BaileyBrookes/Part_IIB_Project/Code/Plots/11-11-18_Base_Still_Satellties.png

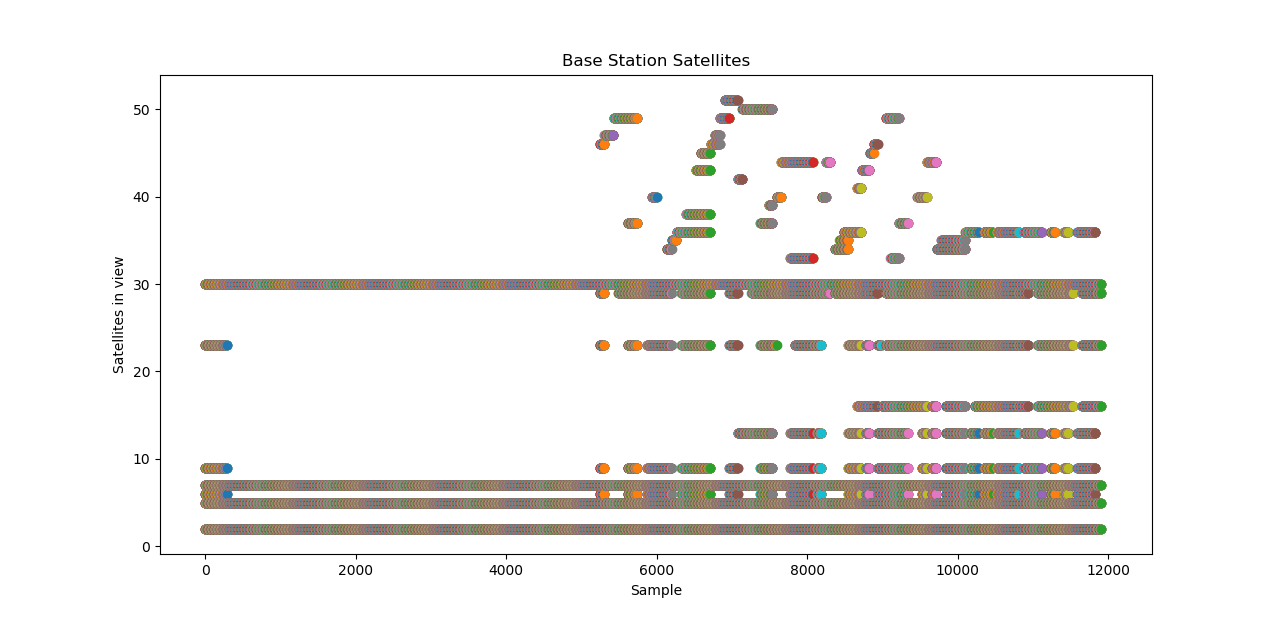
Code/Plots/11-11-18_Base_Still_Satellties.png
