BaileyBrookes/Part_IIB_Project/Code/Plots/11-11-18_WALK.png

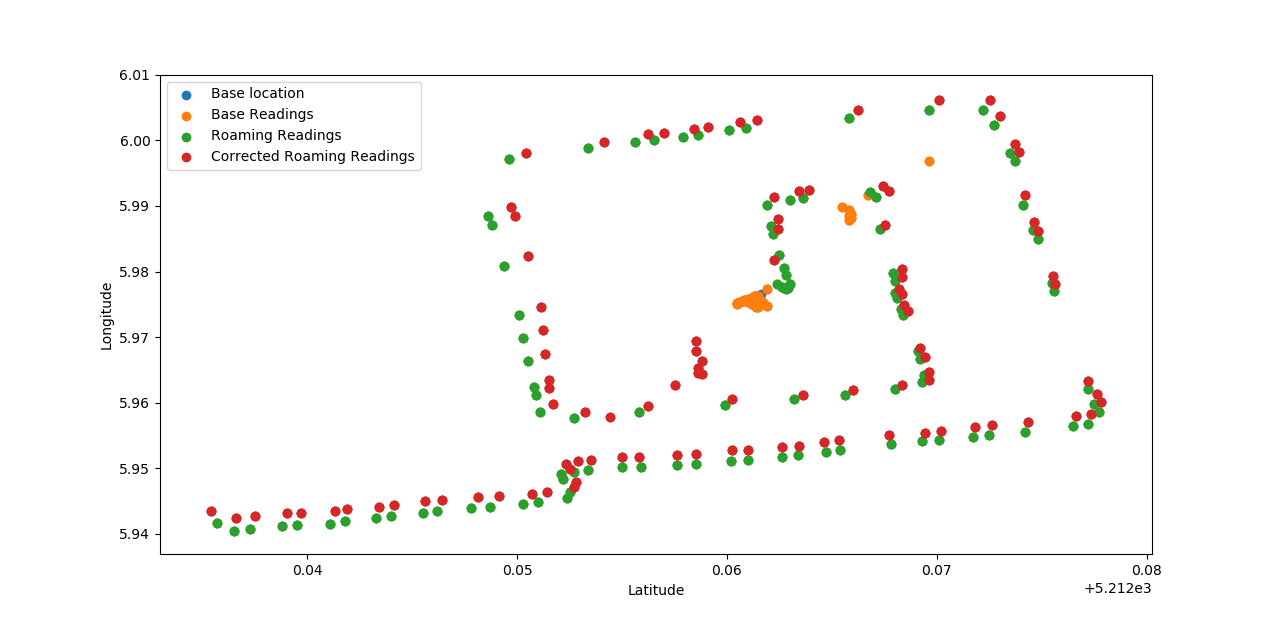
Code/Plots/11-11-18_WALK.png
