BaileyBrookes/Part_IIB_Project/Code/Plots/Figure_1.png

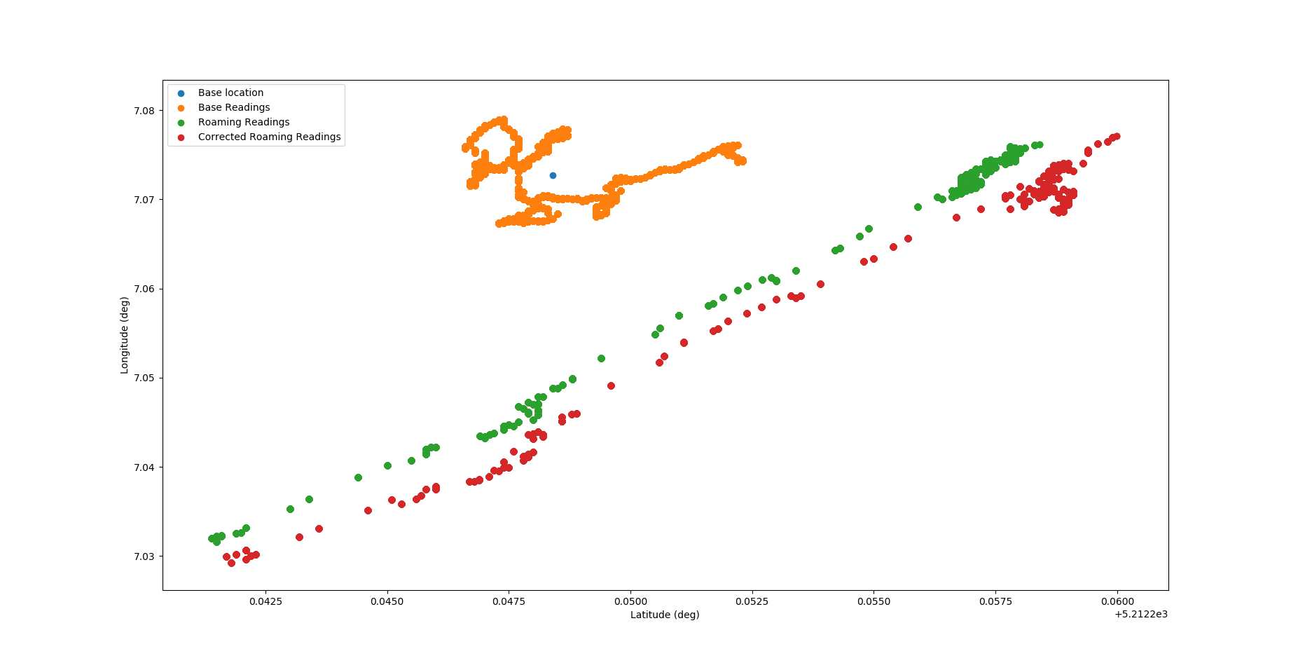
Code/Plots/Figure_1.png
