BaileyBrookes/Part_IIB_Project/Final Report/Castle_hill.png

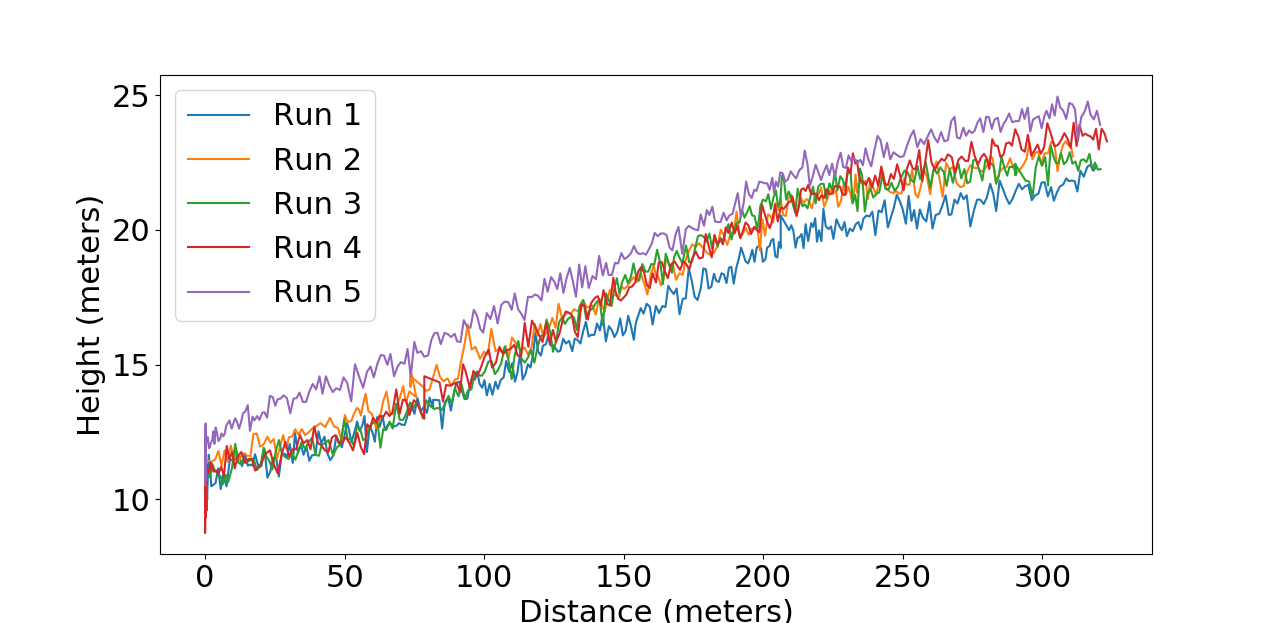
Final Report/Castle_hill.png
