BaileyBrookes/Part_IIB_Project/Final Report/Circuit_annotate.png

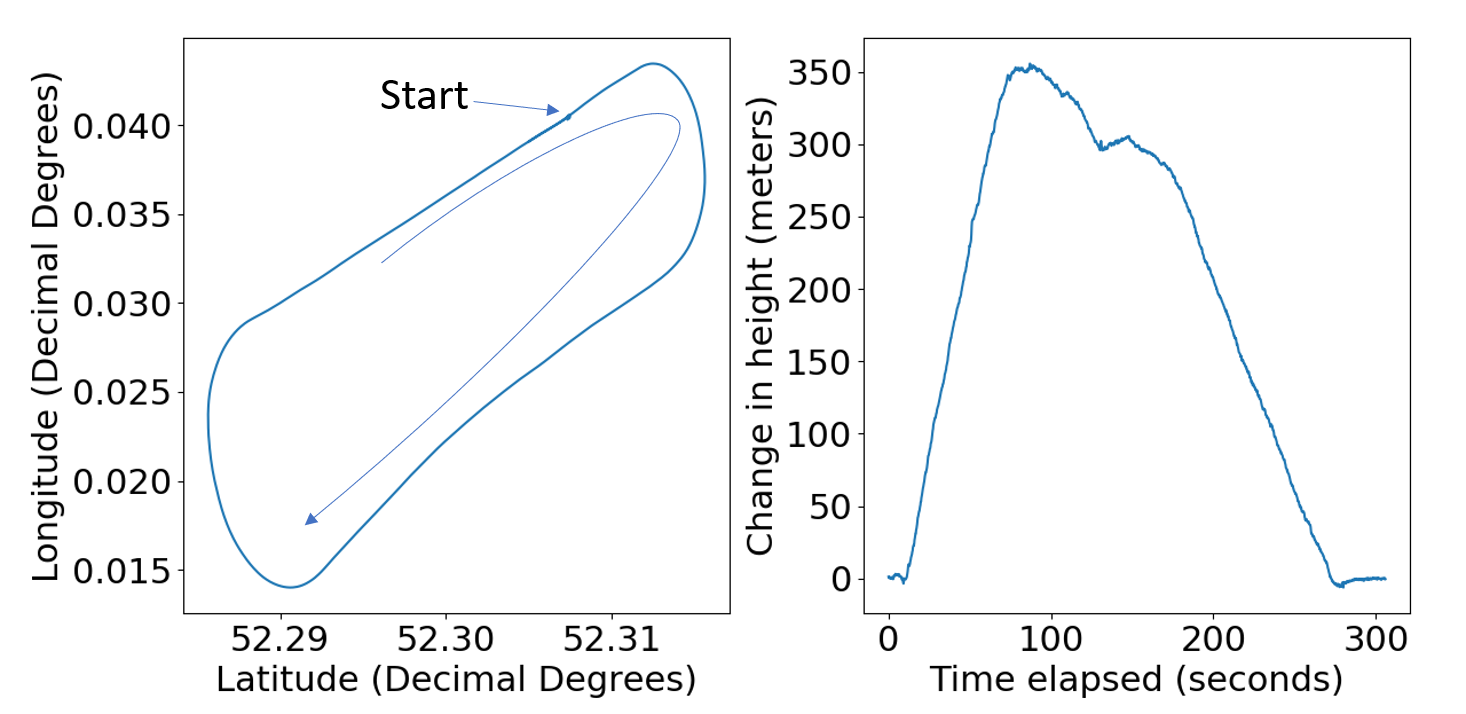
Final Report/Circuit_annotate.png
