BaileyBrookes/Part_IIB_Project/Final Report/Circuit_schematic.png

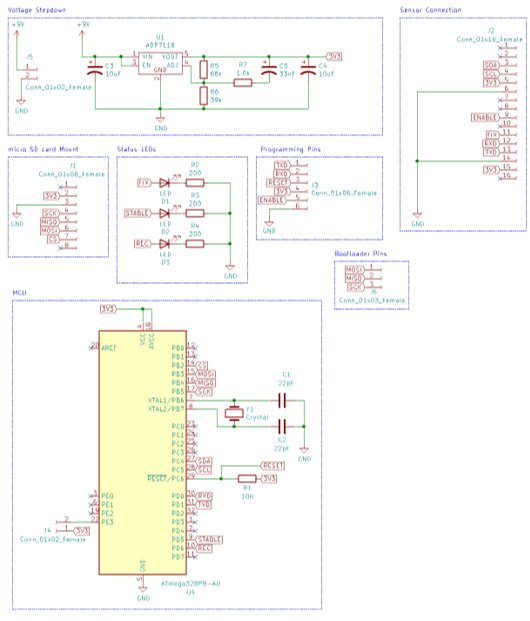
Final Report/Circuit_schematic.png
