BaileyBrookes/Part_IIB_Project/Final Report/Flight_path.png

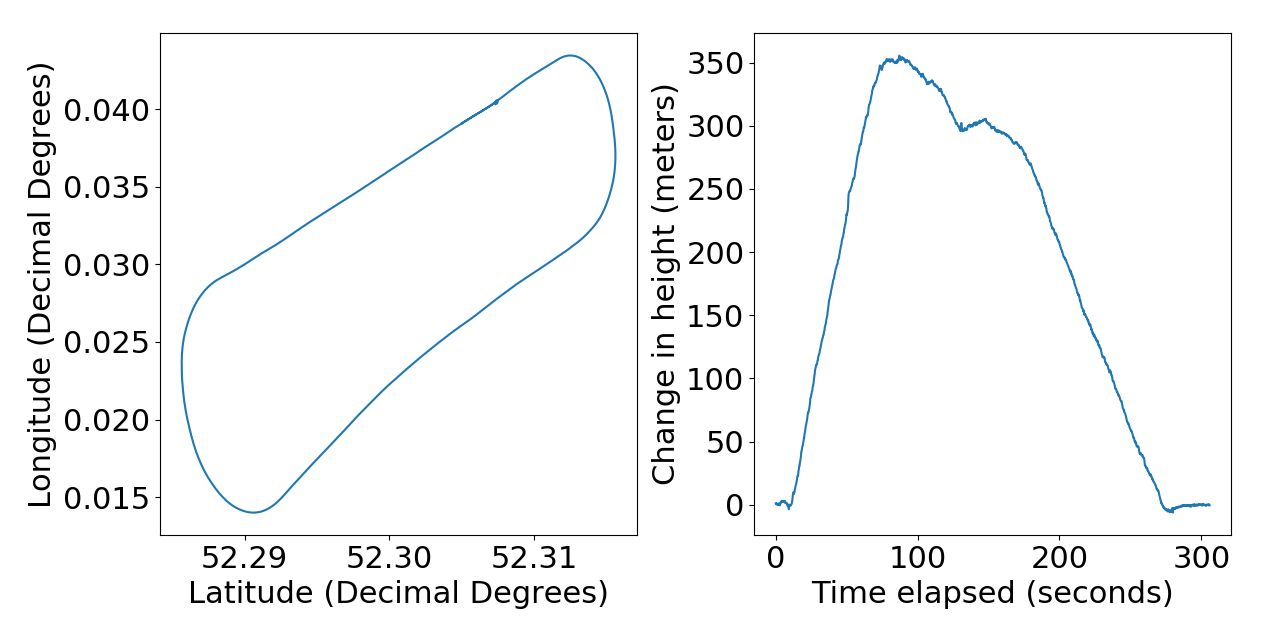
Final Report/Flight_path.png
