BaileyBrookes/Part_IIB_Project/Final Report/GPS_and_altimeter_height.png

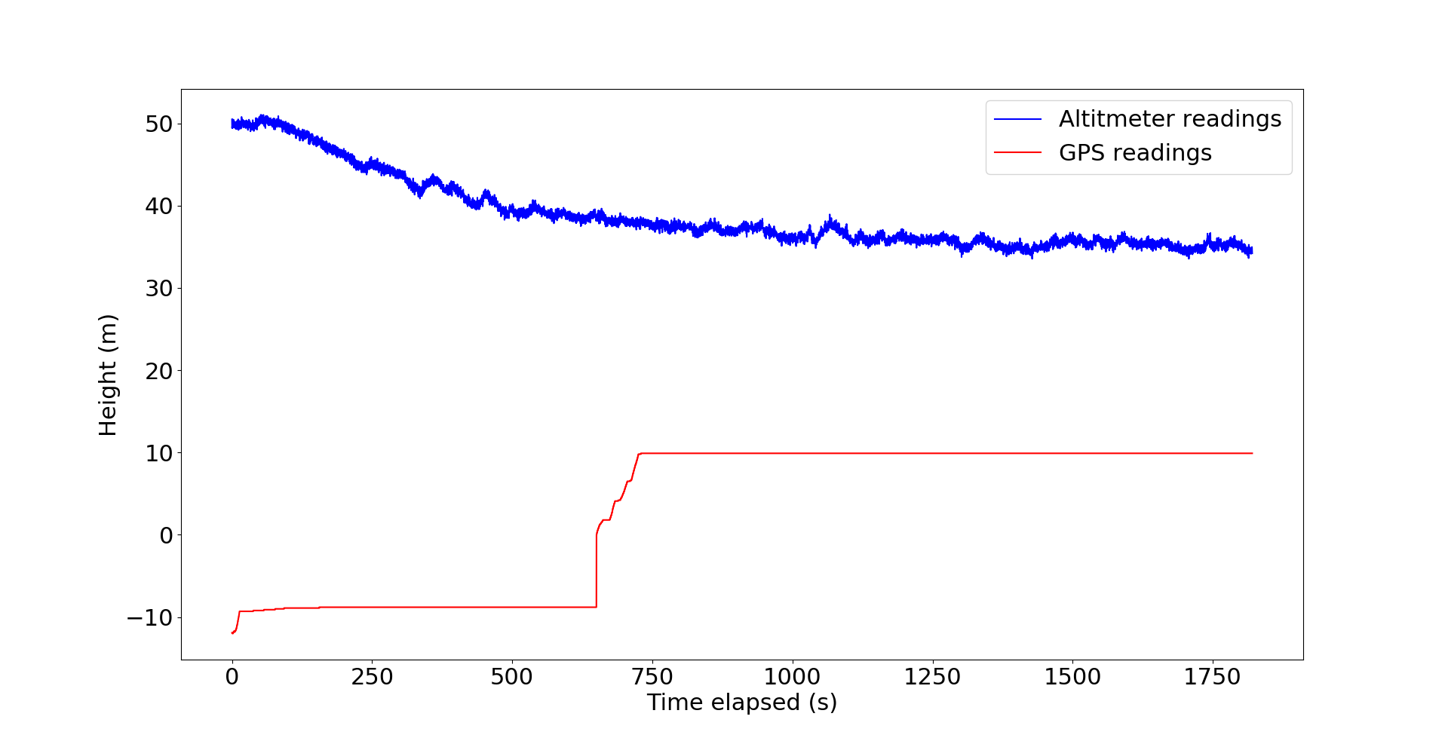
Final Report/GPS_and_altimeter_height.png
