BaileyBrookes/Part_IIB_Project/Final Report/IMG_20190519_162821.jpg

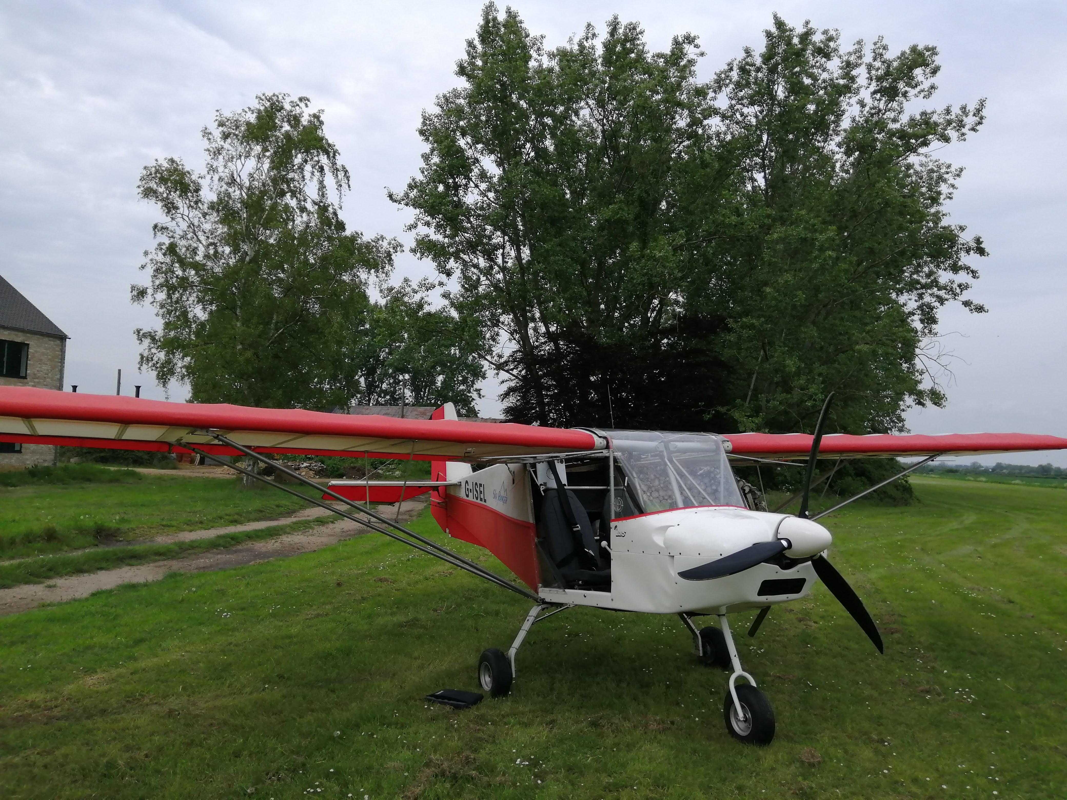
Final Report/IMG_20190519_162821.jpg
