BaileyBrookes/Part_IIB_Project/Final Report/IMG_20190520_114710.jpg

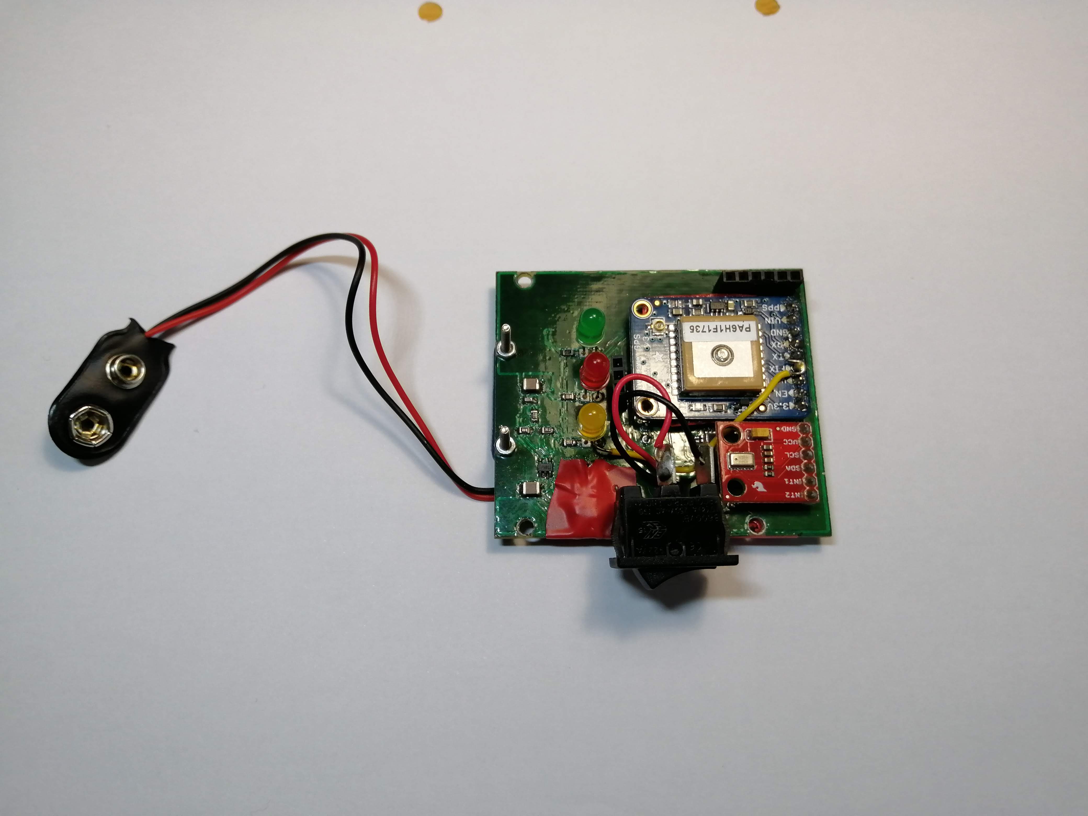
Final Report/IMG_20190520_114710.jpg
