BaileyBrookes/Part_IIB_Project/Final Report/IMG_20190520_114843.jpg

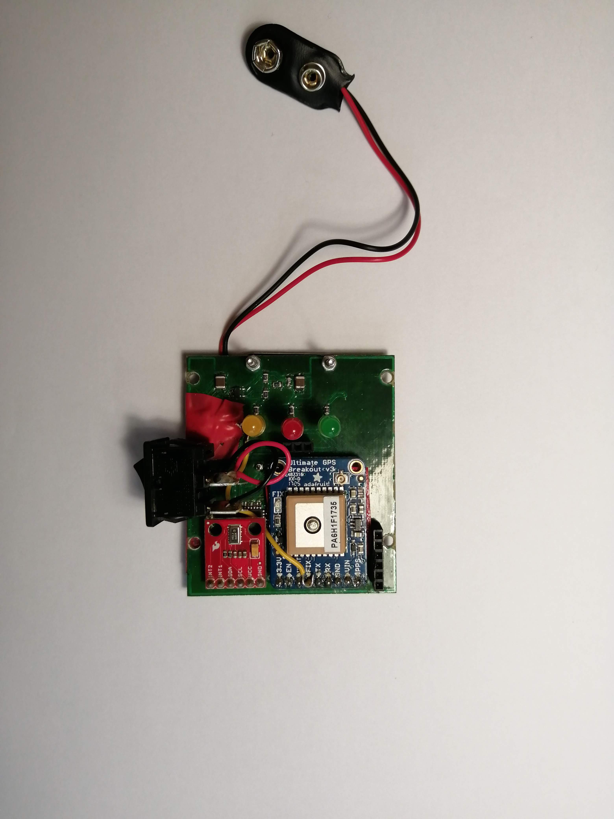
Final Report/IMG_20190520_114843.jpg
