BaileyBrookes/Part_IIB_Project/Final Report/IMG_20190520_114852.jpg

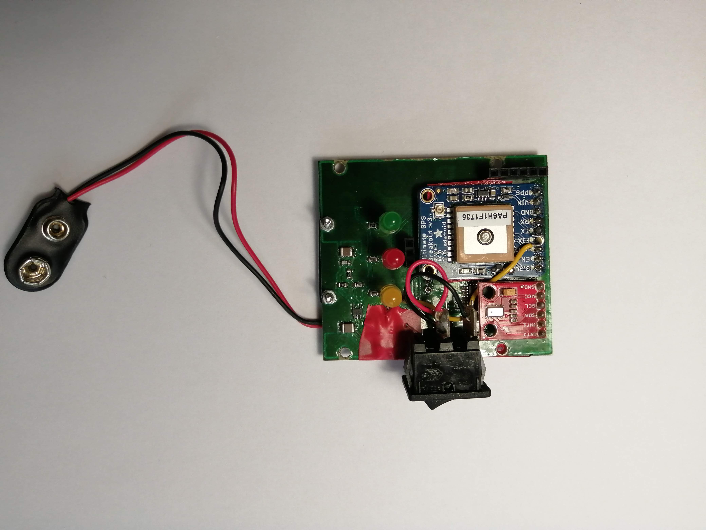
Final Report/IMG_20190520_114852.jpg
