BaileyBrookes/Part_IIB_Project/Final Report/IMG_20190520_115139.jpg

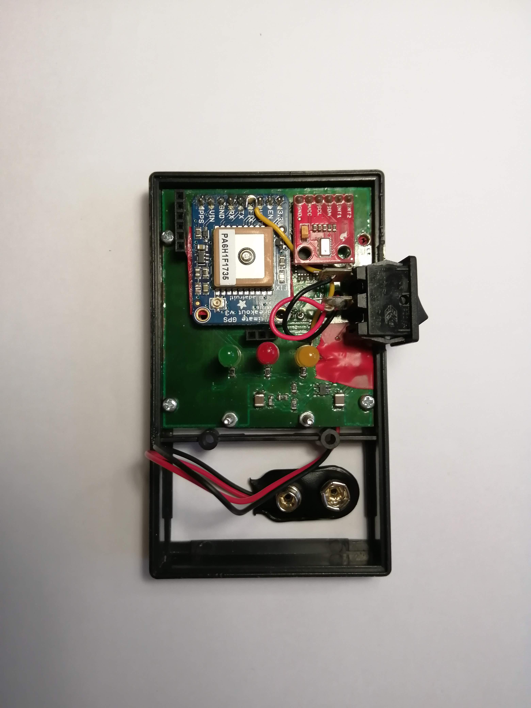
Final Report/IMG_20190520_115139.jpg
