BaileyBrookes/Part_IIB_Project/Final Report/IMG_20190520_115651.jpg

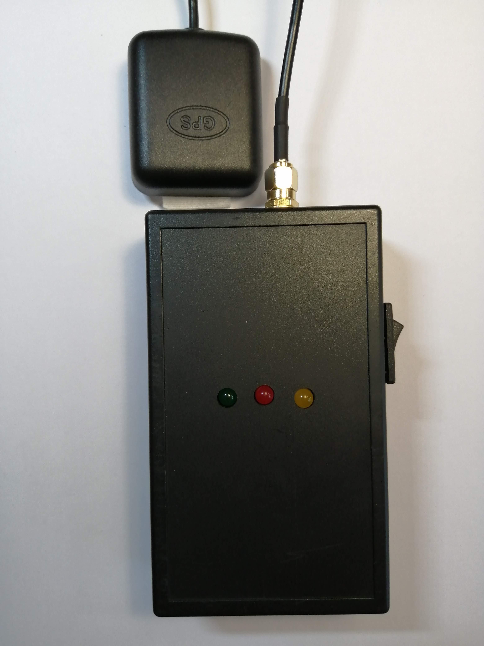
Final Report/IMG_20190520_115651.jpg
