BaileyBrookes/Part_IIB_Project/Final Report/jump.png

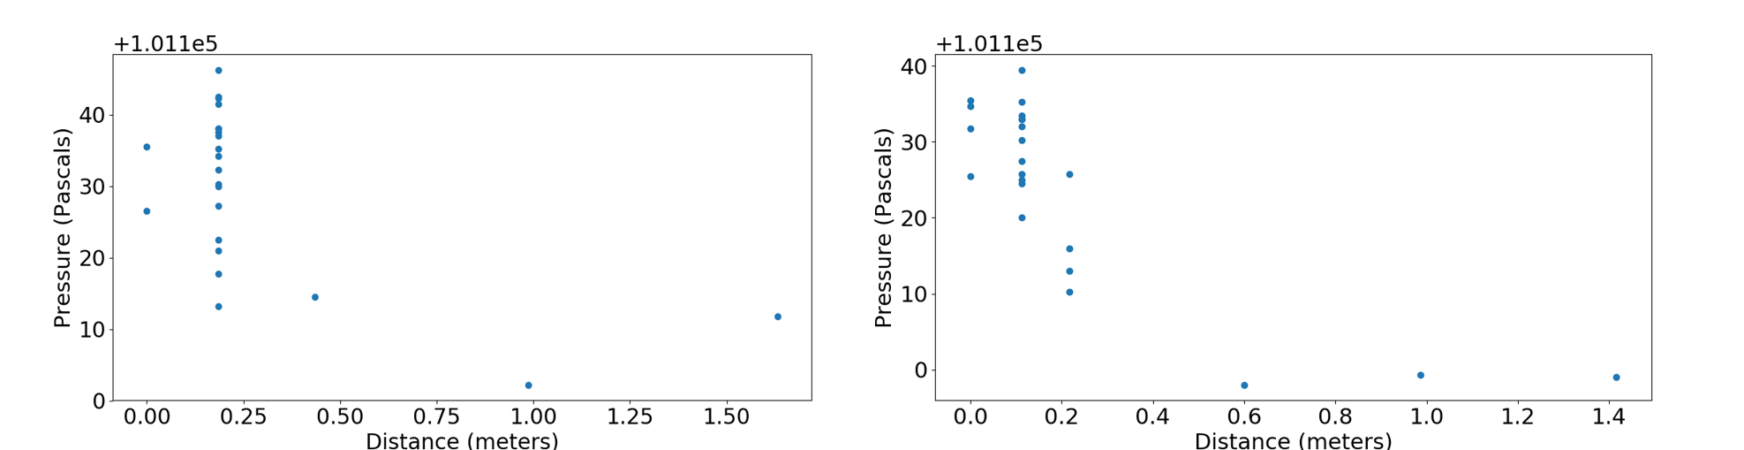
Final Report/jump.png
