BaileyBrookes/Part_IIB_Project/Final Report/Landing_flight_1.png

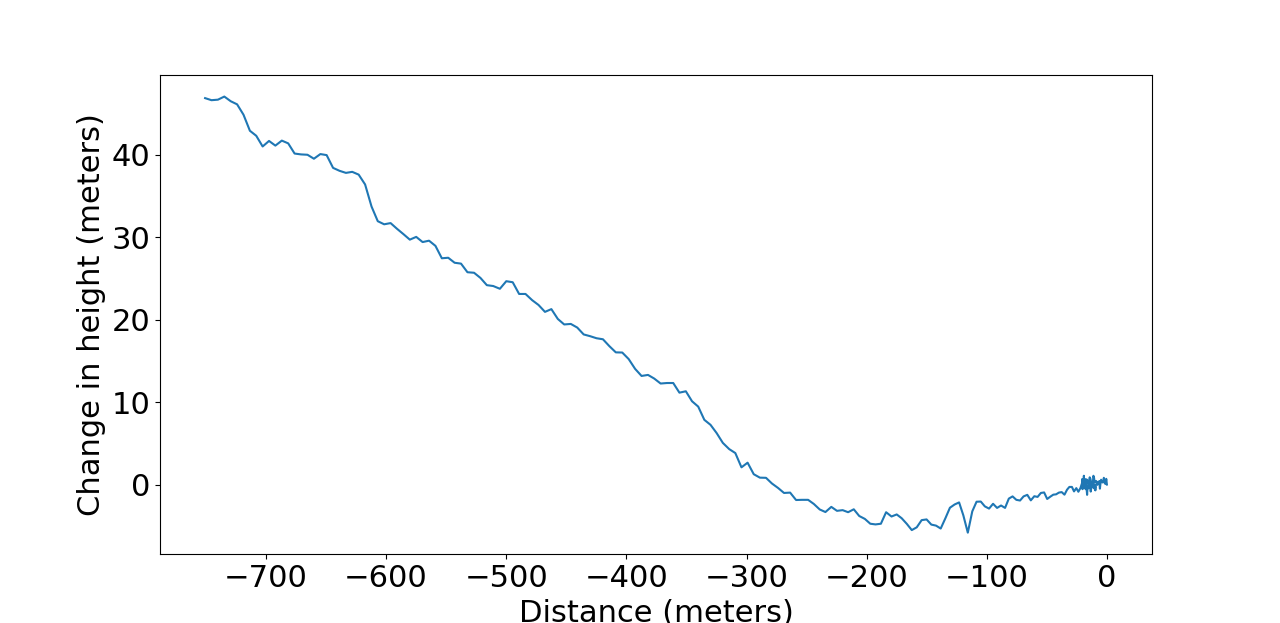
Final Report/Landing_flight_1.png
