BaileyBrookes/Part_IIB_Project/Final Report/Leck_100m_4.png

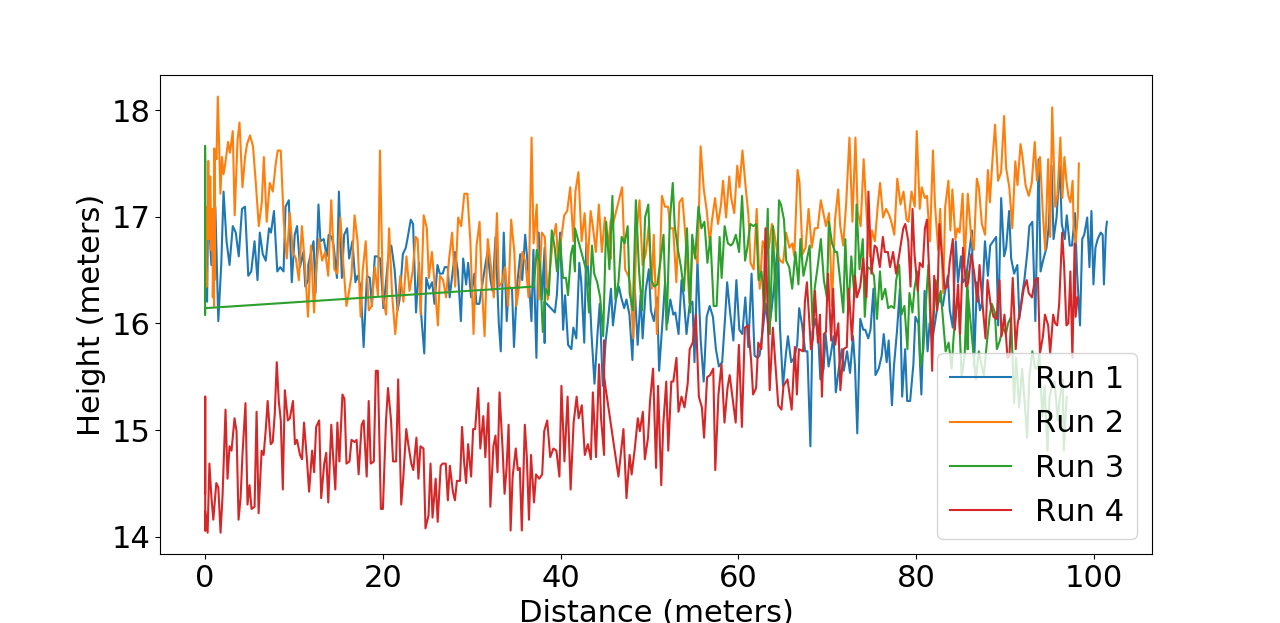
Final Report/Leck_100m_4.png
