BaileyBrookes/Part_IIB_Project/Final Report/Leck_GPS_Pres.png

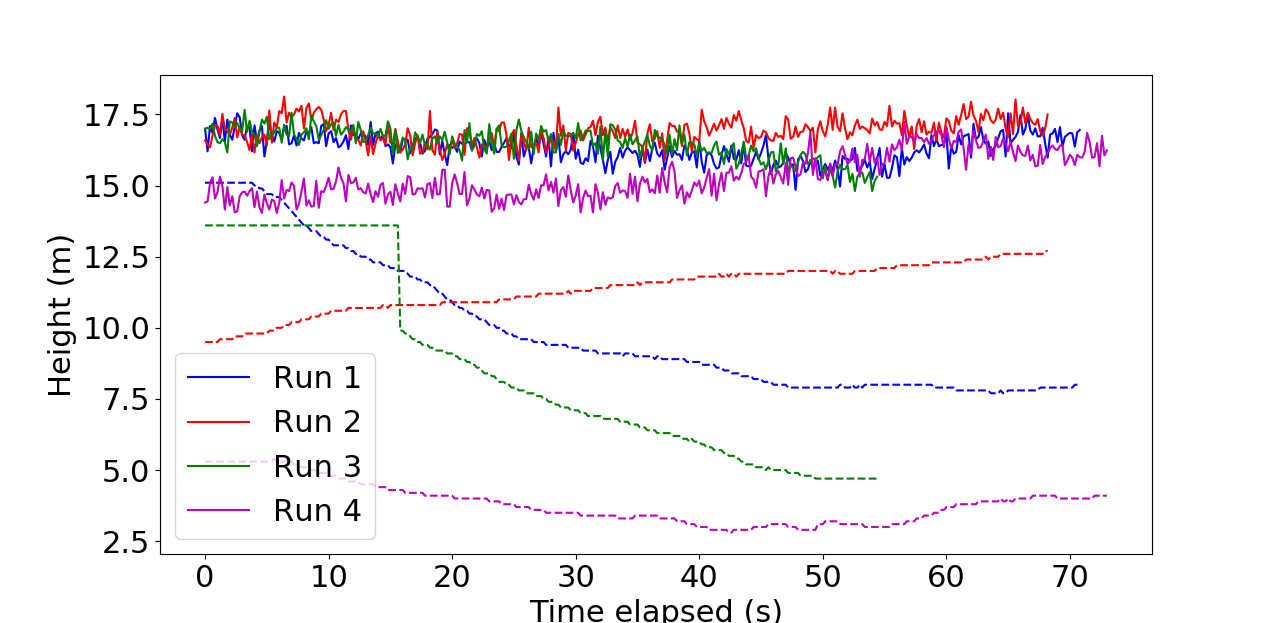
Final Report/Leck_GPS_Pres.png
