BaileyBrookes/Part_IIB_Project/Final Report/LED_status.png

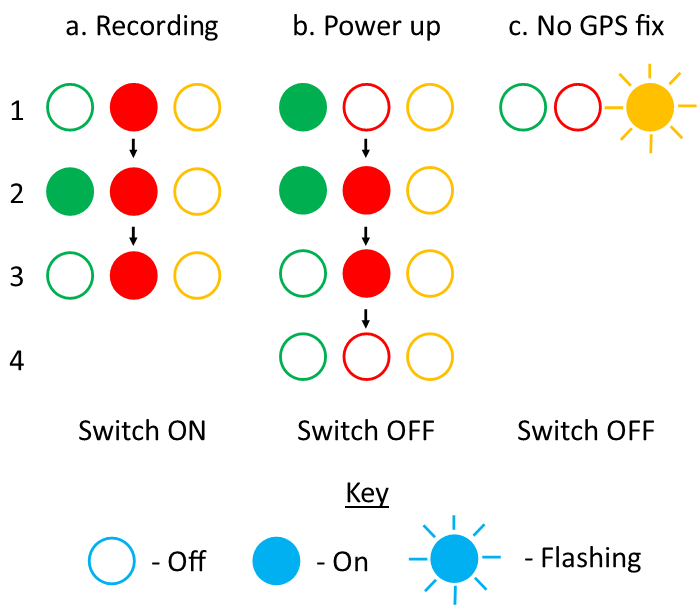
Final Report/LED_status.png
