BaileyBrookes/Part_IIB_Project/Final Report/Level_height.png

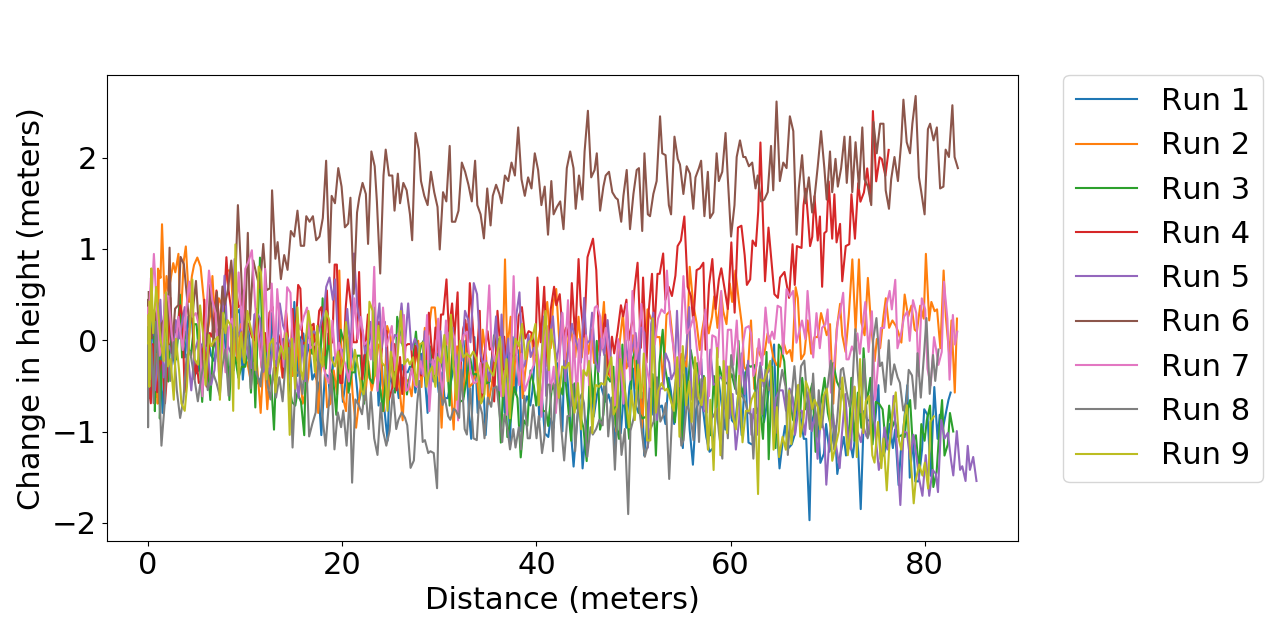
Final Report/Level_height.png
