BaileyBrookes/Part_IIB_Project/Final Report/PCB.png

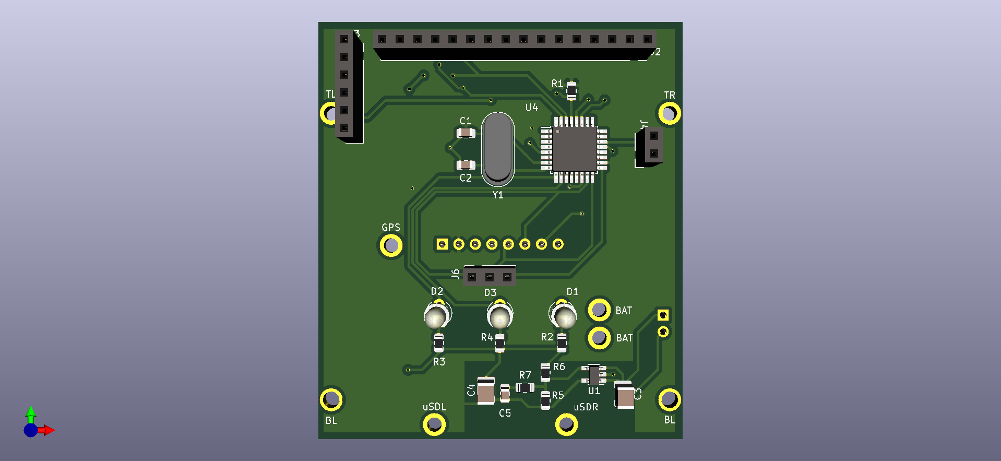
Final Report/PCB.png
