BaileyBrookes/Part_IIB_Project/Final Report/Run_1.png

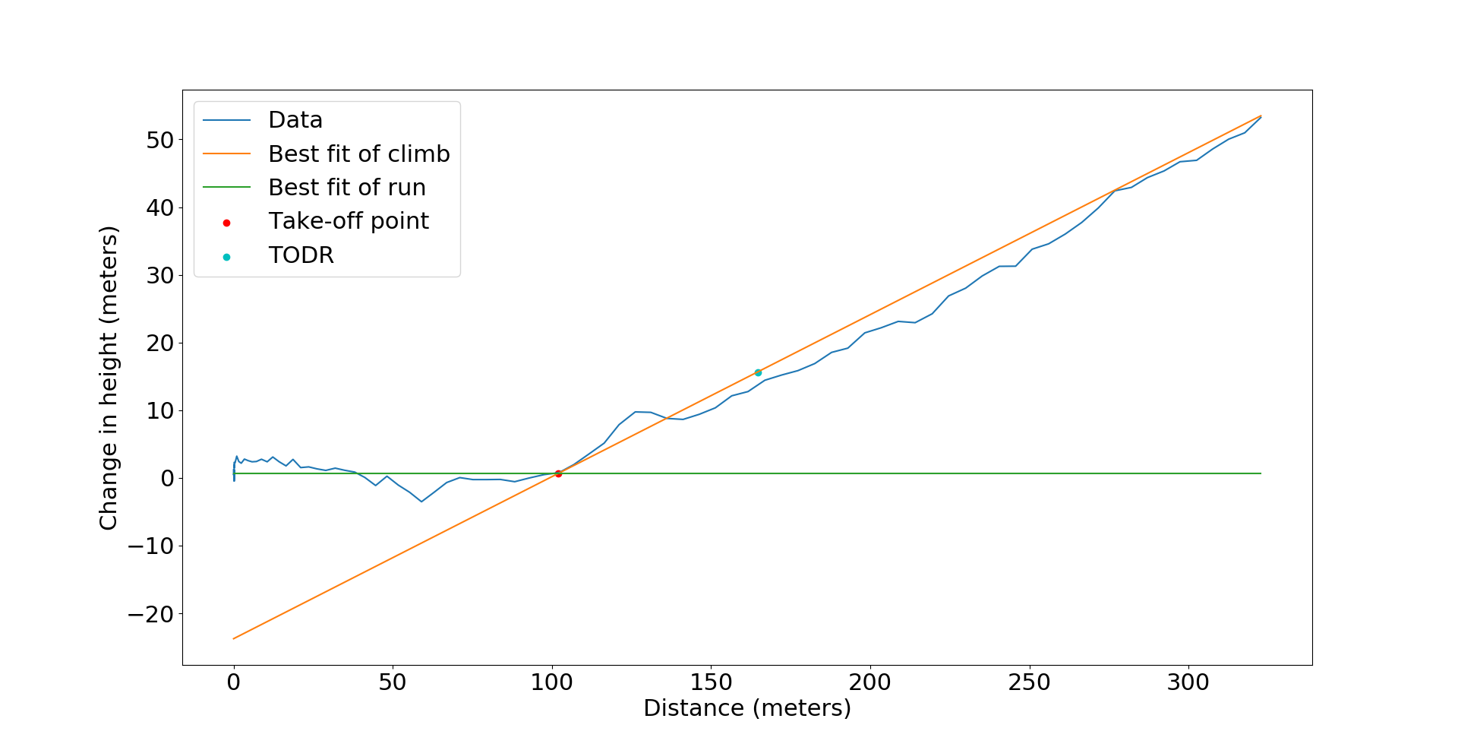
Final Report/Run_1.png
