BaileyBrookes/Part_IIB_Project/Final Report/Run_1_jump.png

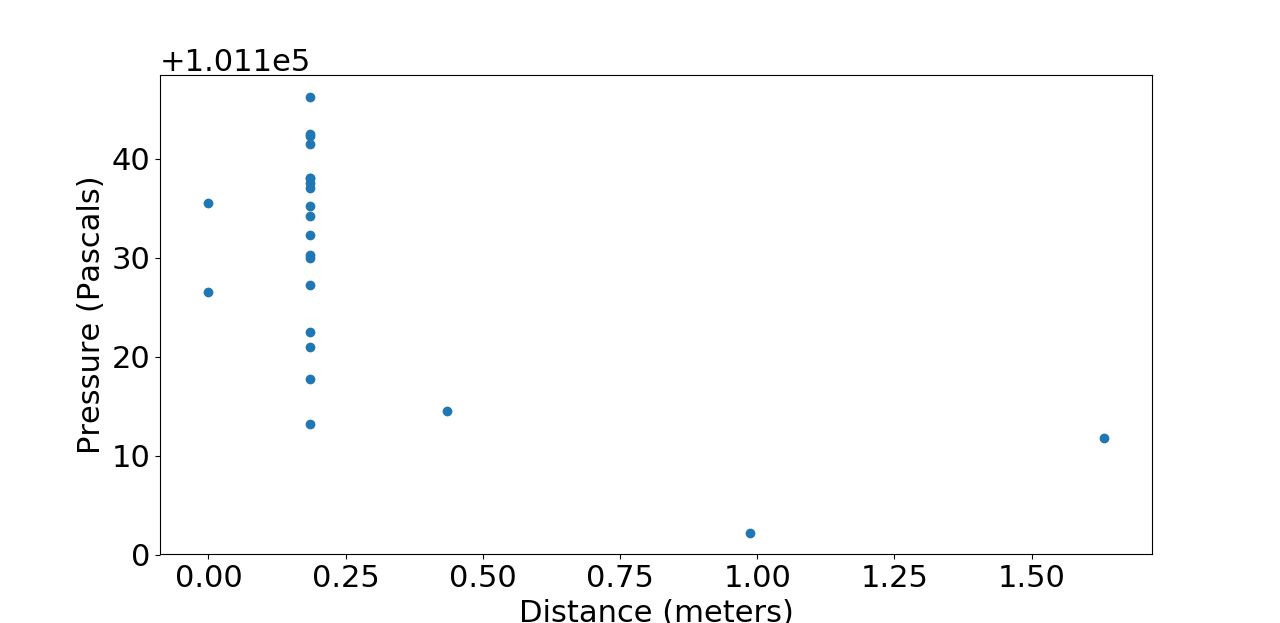
Final Report/Run_1_jump.png
