BaileyBrookes/Part_IIB_Project/Final Report/Run_2.png

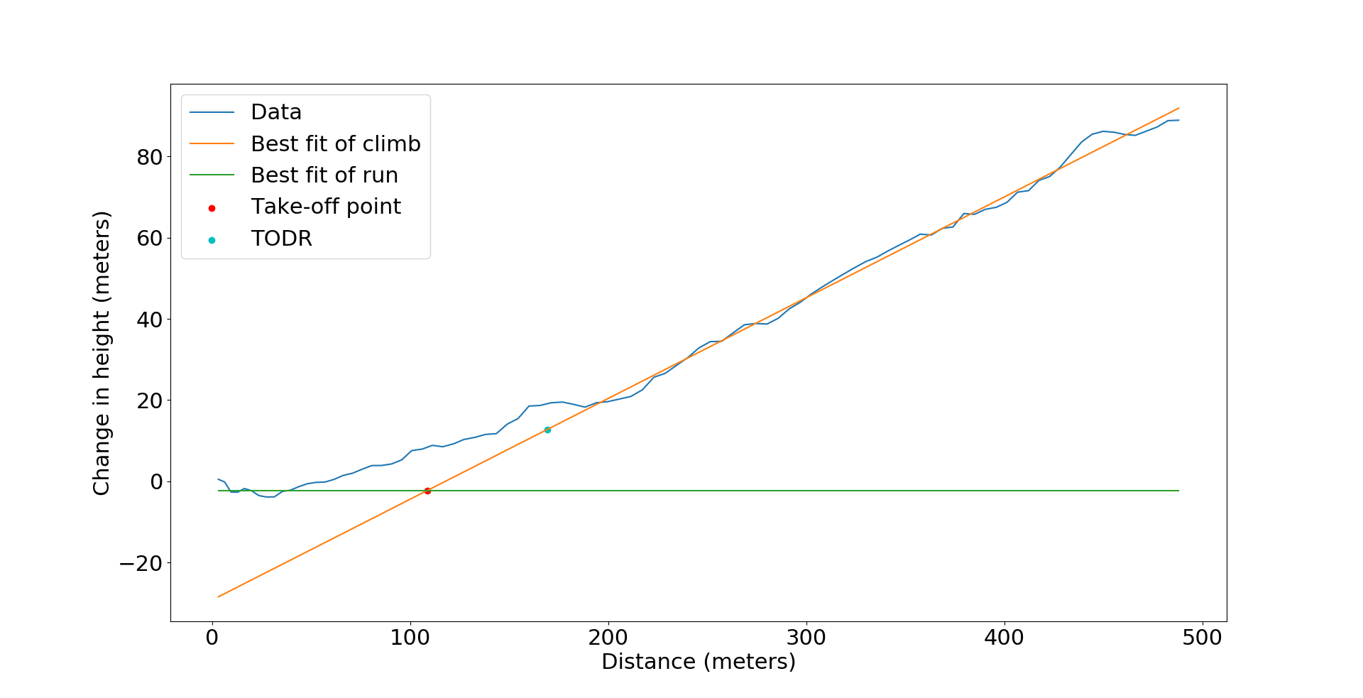
Final Report/Run_2.png
