BaileyBrookes/Part_IIB_Project/Final Report/Run_3_jump.png

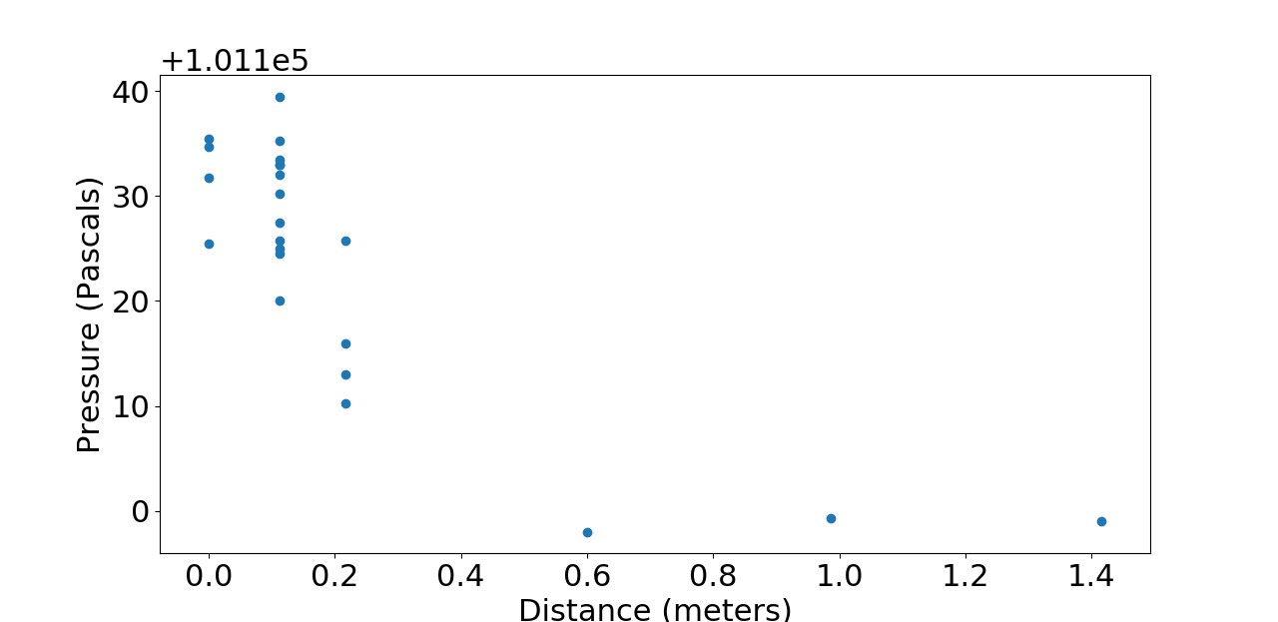
Final Report/Run_3_jump.png
