BaileyBrookes/Part_IIB_Project/Final Report/Schematic.png

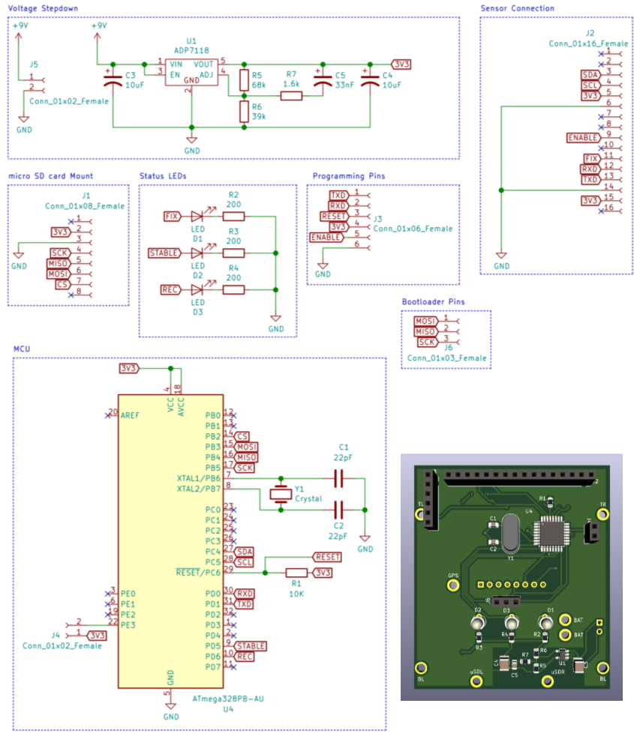
Final Report/Schematic.png
