BaileyBrookes/Part_IIB_Project/Final Report/speed_v_pressure.png

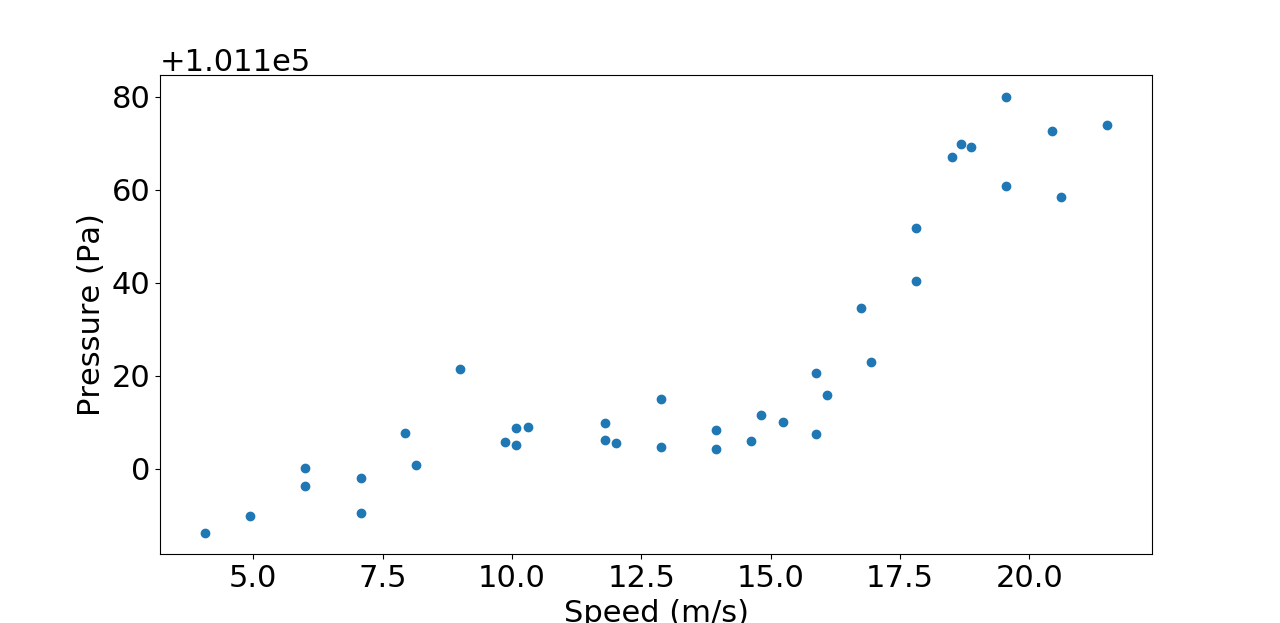
Final Report/speed_v_pressure.png
