BaileyBrookes/Part_IIB_Project/Final Report/Static_pressure_temperture.png

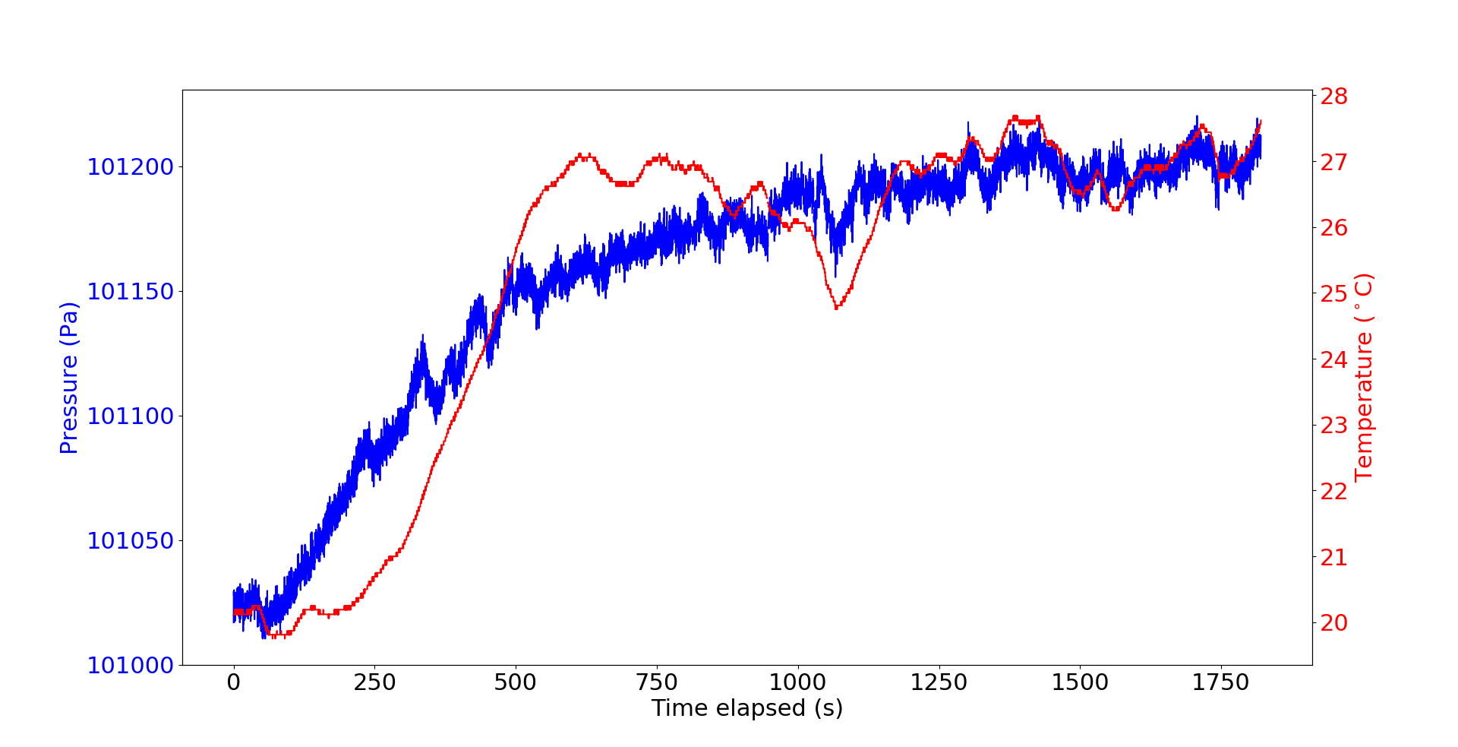
Final Report/Static_pressure_temperture.png
