BaileyBrookes/Part_IIB_Project/Final Report/TODR_data.png

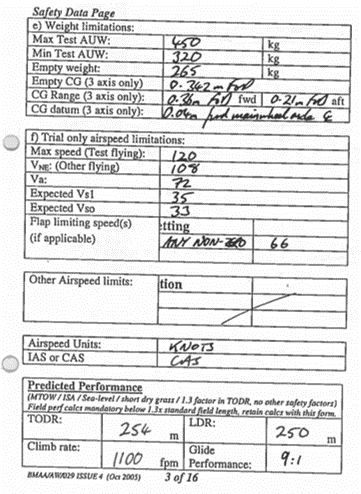
Final Report/TODR_data.png
