BaileyBrookes/Part_IIB_Project/Final Report/Trig_method.jpg

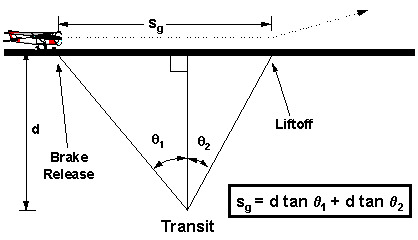
Final Report/Trig_method.jpg
