BaileyBrookes/Part_IIB_Project/Mich Presentation/4V0G4.png

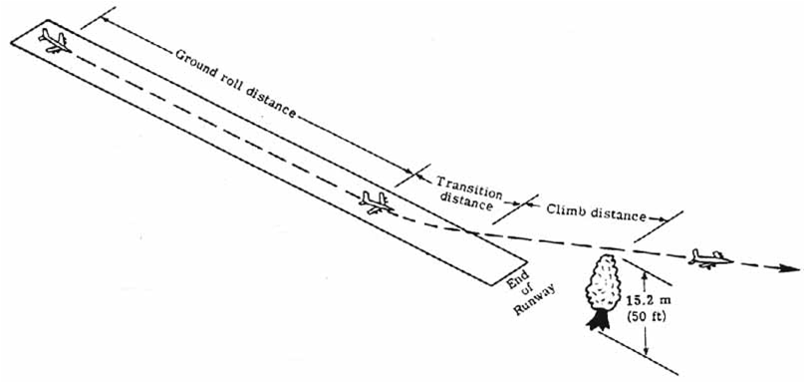
Mich Presentation/4V0G4.png
