BaileyBrookes/Part_IIB_Project/Mich Presentation/5m.png

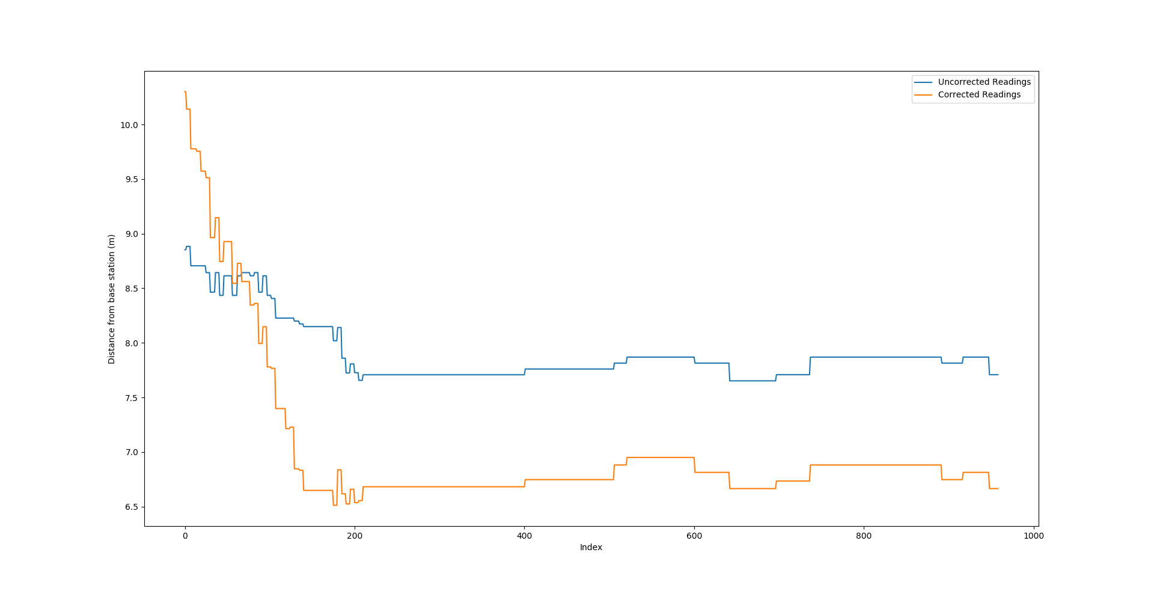
Mich Presentation/5m.png
