BaileyBrookes/Part_IIB_Project/Mich Presentation/50m.png

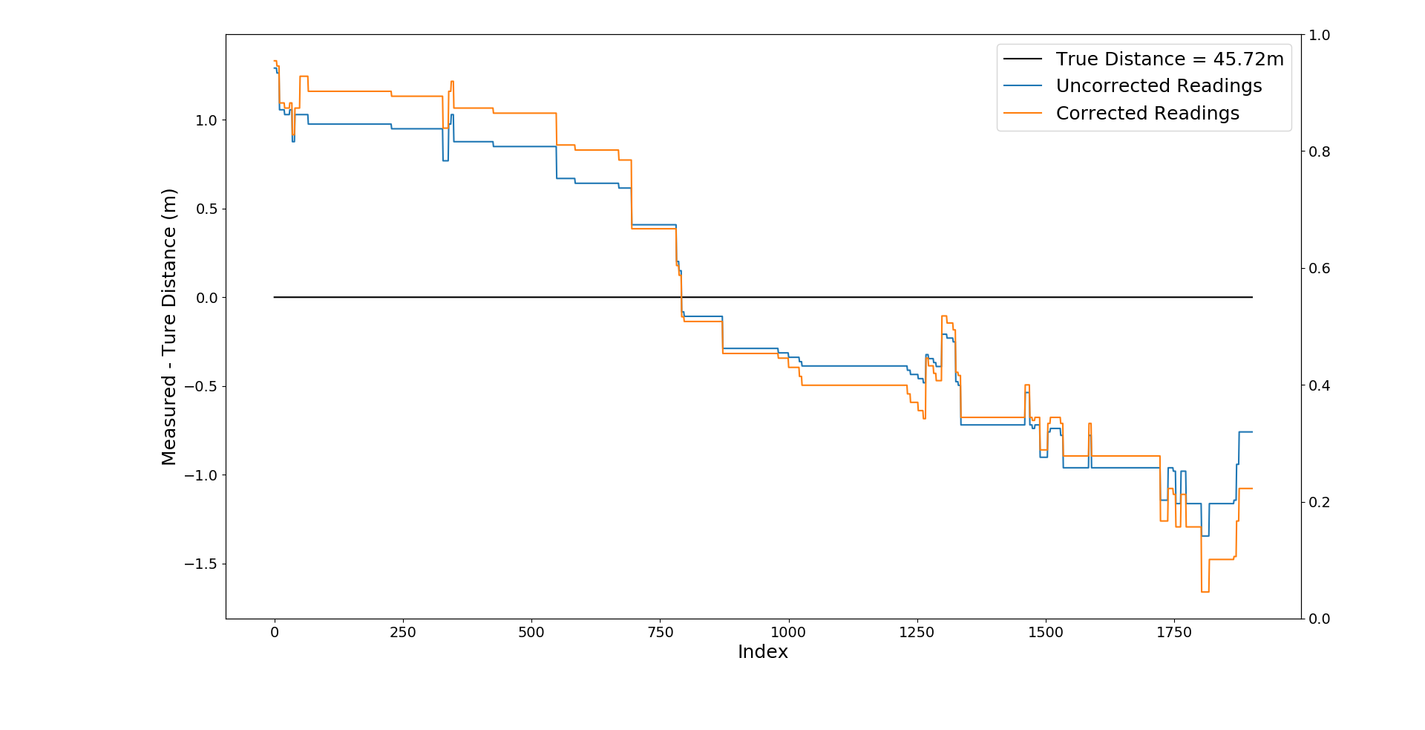
Mich Presentation/50m.png
