BaileyBrookes/Part_IIB_Project/Mich Presentation/50m_latlon.png

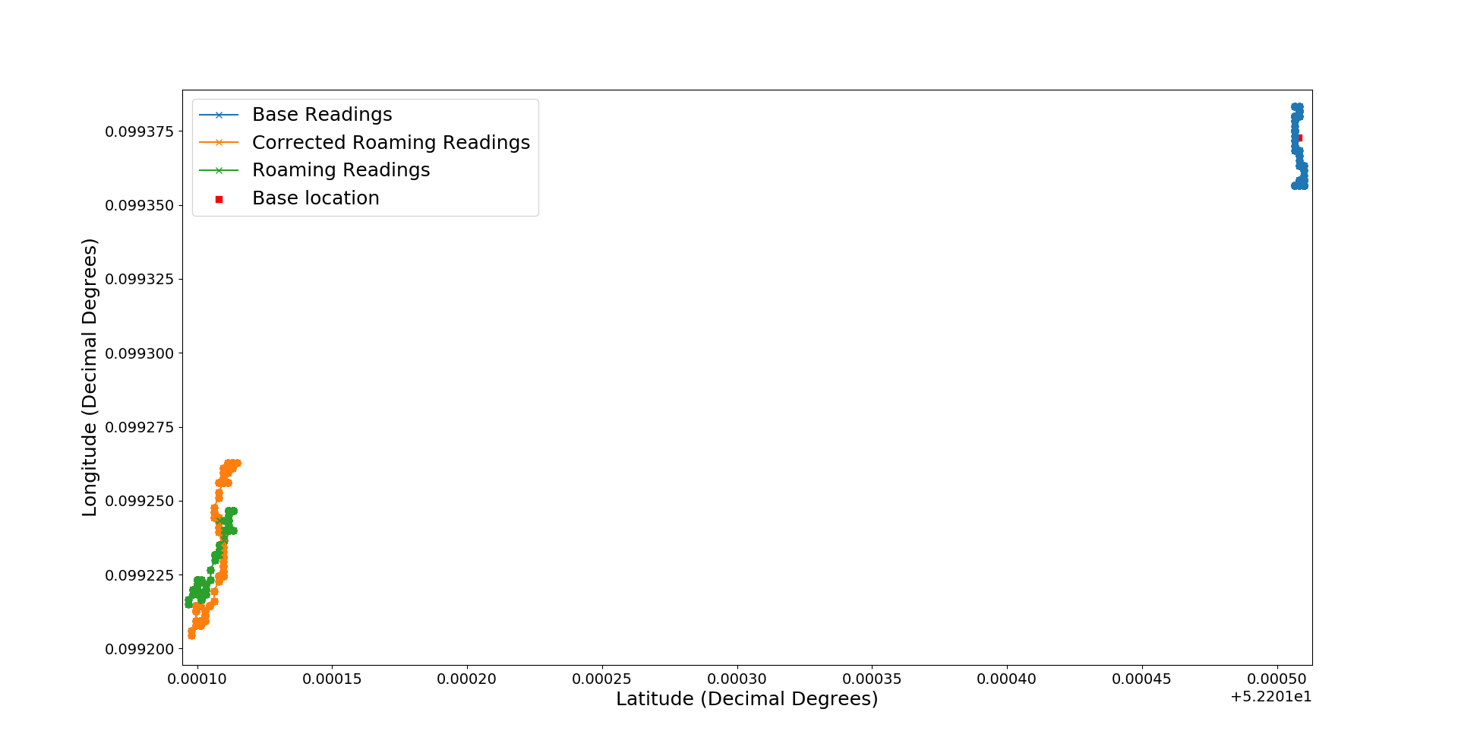
Mich Presentation/50m_latlon.png
