BaileyBrookes/Part_IIB_Project/Mich Presentation/100m.png

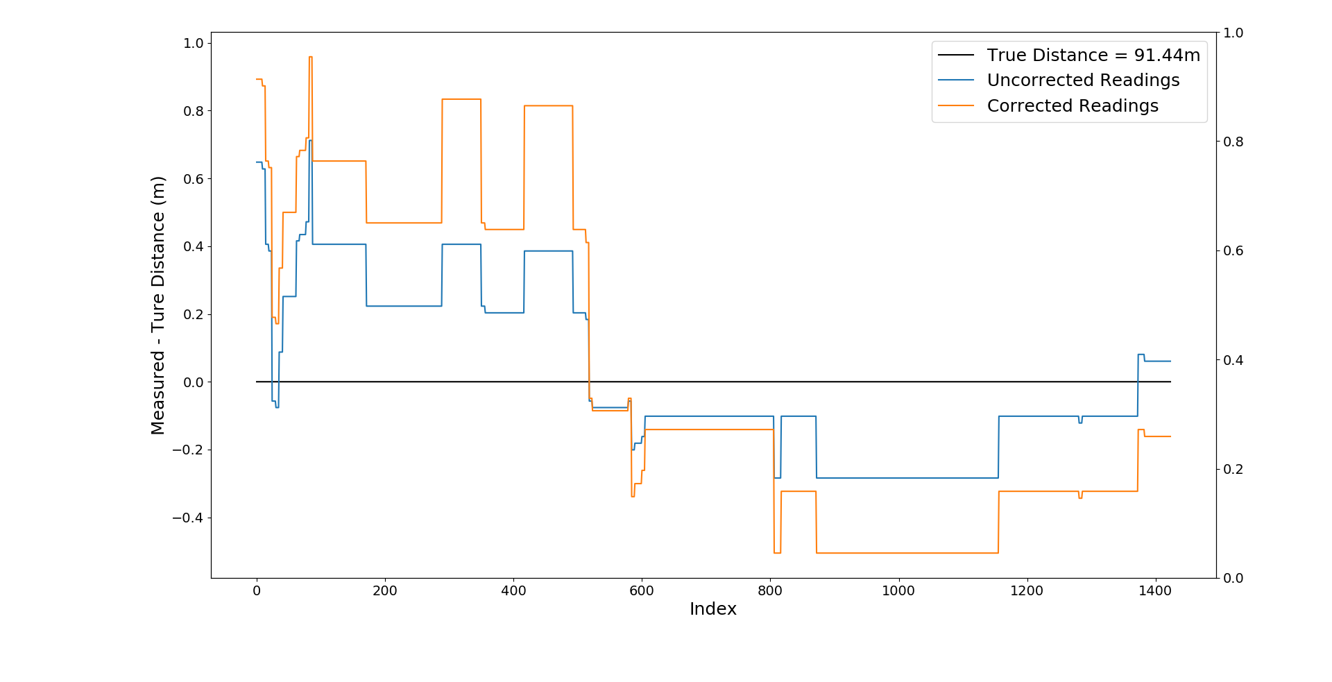
Mich Presentation/100m.png
