BaileyBrookes/Part_IIB_Project/Mich Presentation/DGPS-System2.jpg

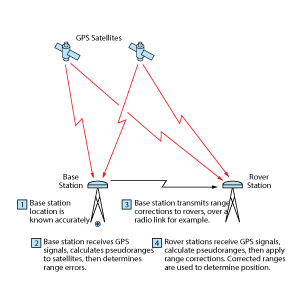
Mich Presentation/DGPS-System2.jpg
