BaileyBrookes/Part_IIB_Project/Mich Presentation/Pchart.gif

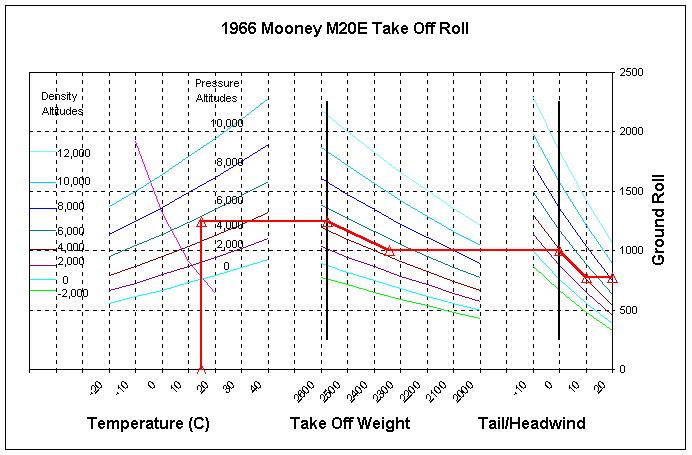
Mich Presentation/Pchart.gif
