BaileyBrookes/Part_IIB_Project/Mich Presentation/Table.jpg

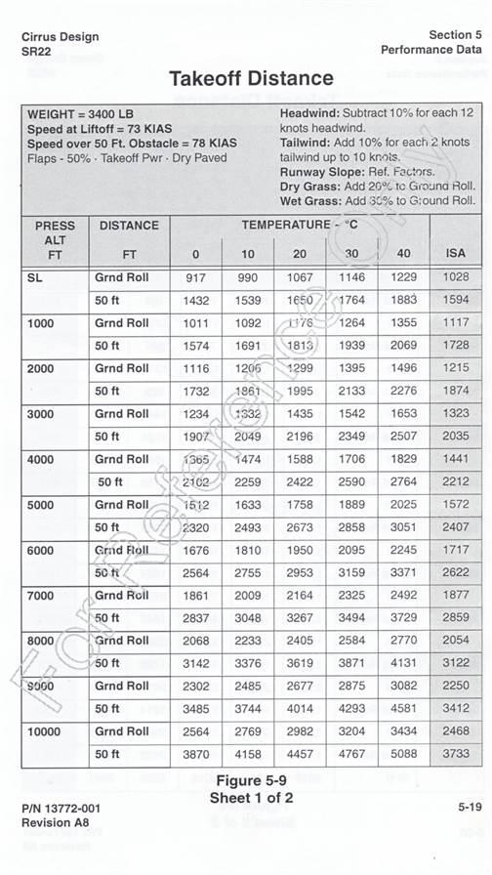
Mich Presentation/Table.jpg
