BaileyBrookes/Part_IIB_Project/Technical Milestone Report/Gantt_Chart.jpg

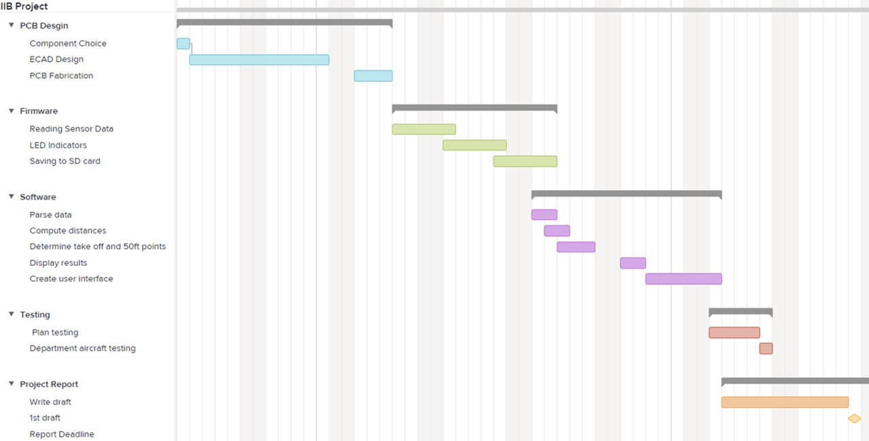
Technical Milestone Report/Gantt_Chart.jpg
