BaileyBrookes/Part_IIB_Project/Technical Milestone Report/Pressure.png

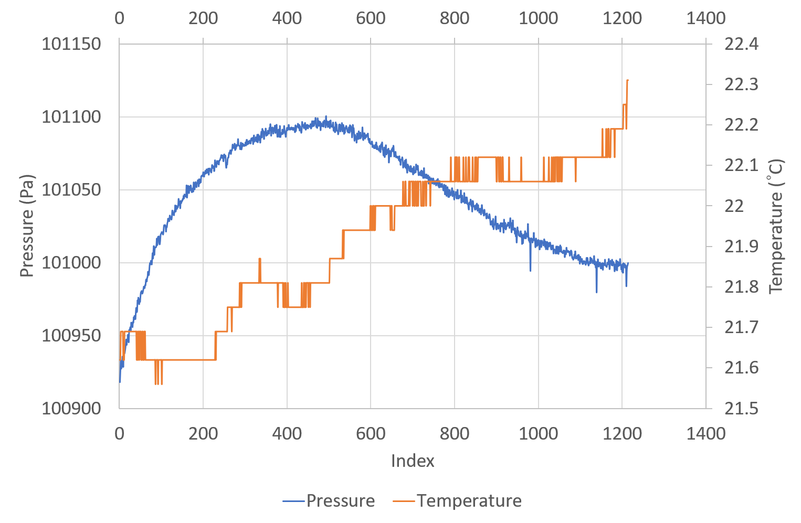
Technical Milestone Report/Pressure.png
