BaileyBrookes/Part_IIB_Project/Technical Milestone Report/100m_test.png

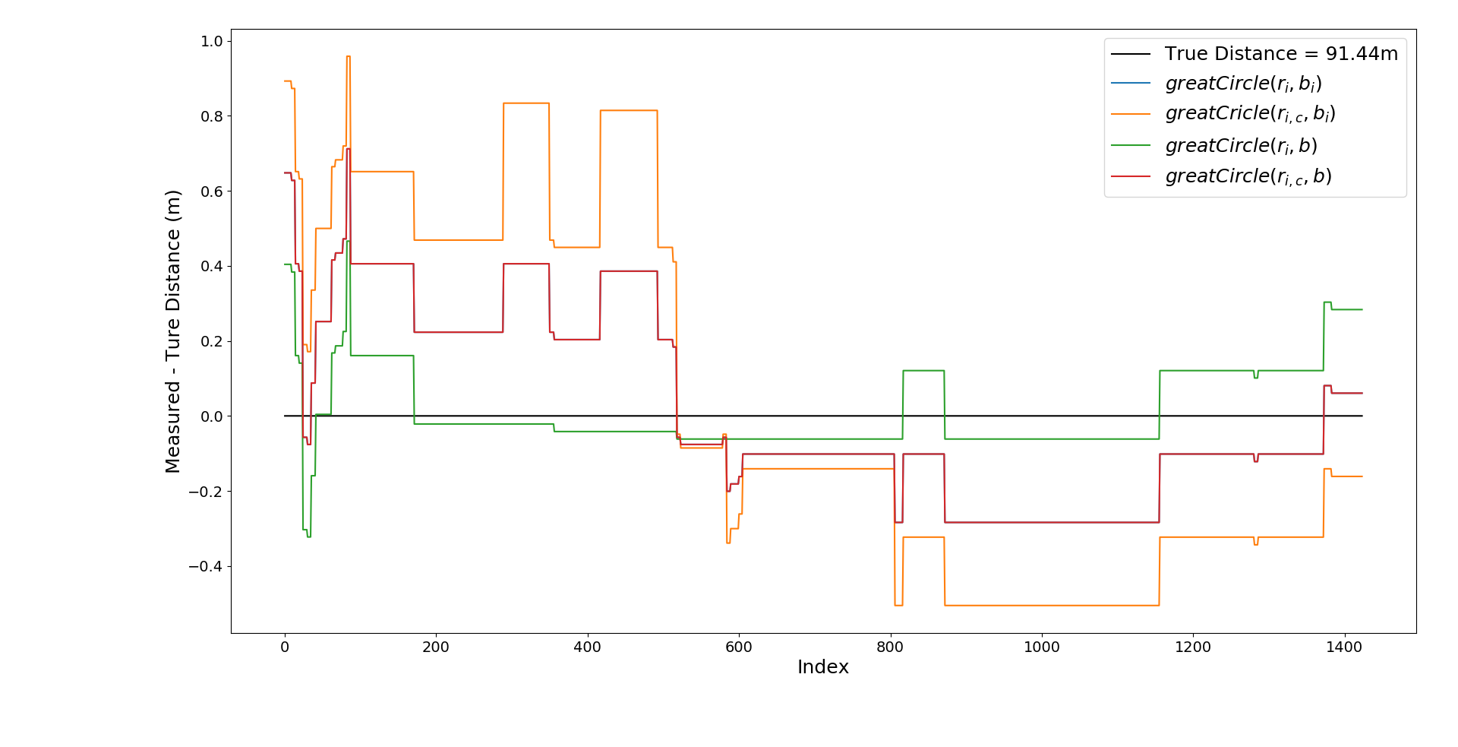
Technical Milestone Report/100m_test.png
