BaileyBrookes/Part_IIB_Project/Technical Milestone Report/Hz_Test.png

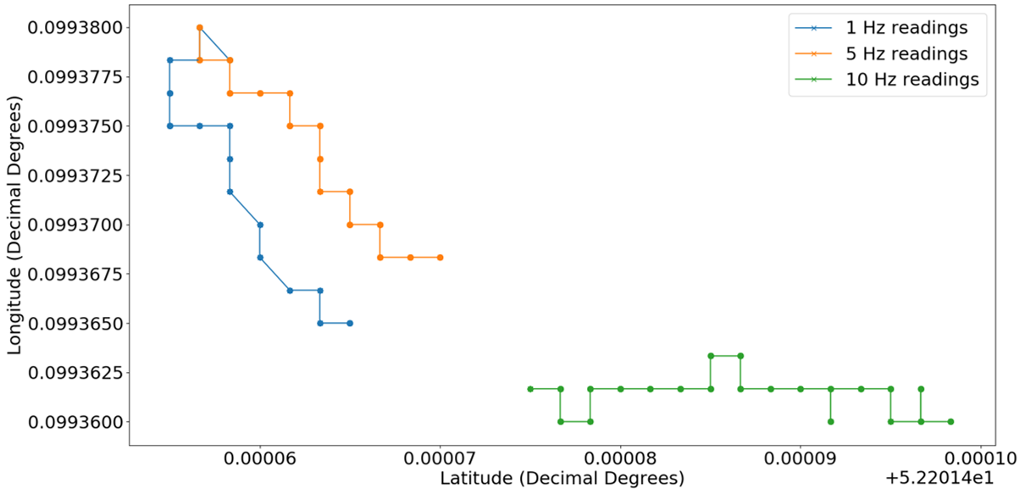
Technical Milestone Report/Hz_Test.png
