BaileyBrookes/Part_IIB_Project/AircraftDataLogger/Manufacture Files v2/AircraftDataLogger-B.Cu.pdf

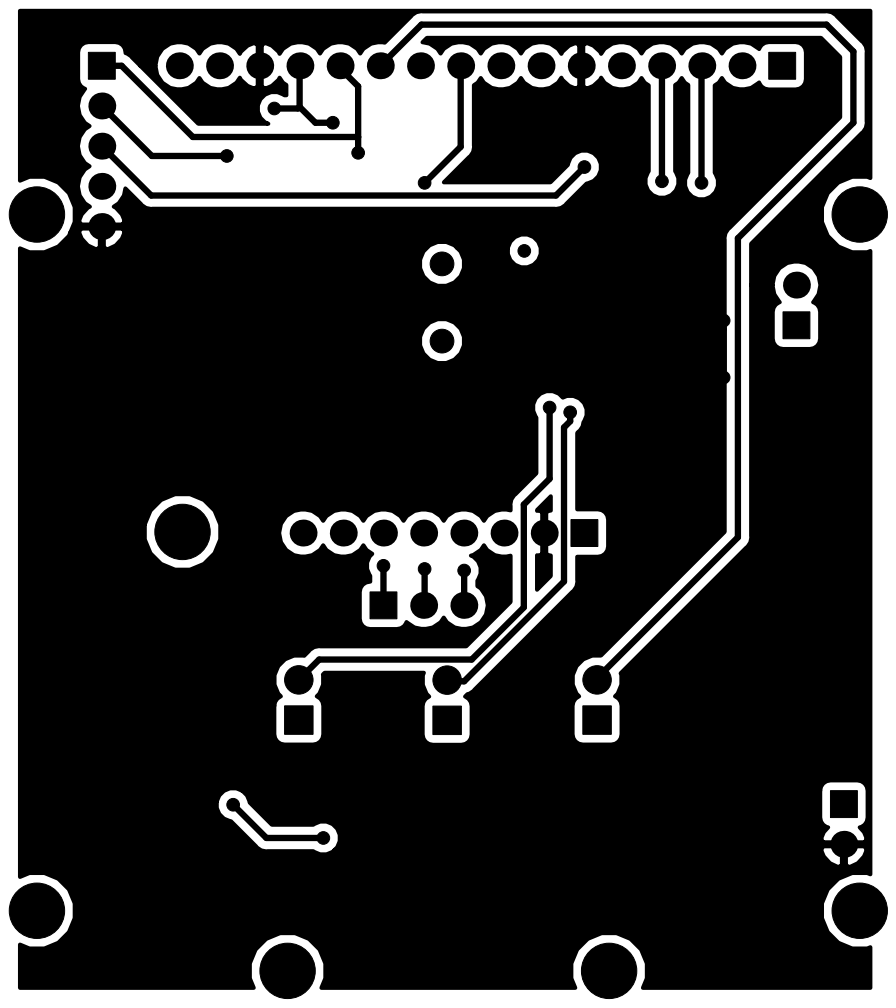
[picture p84: page 1]
