BaileyBrookes/Part_IIB_Project/AircraftDataLogger/Manufacture Files v2/AircraftDataLogger-F.Cu.pdf

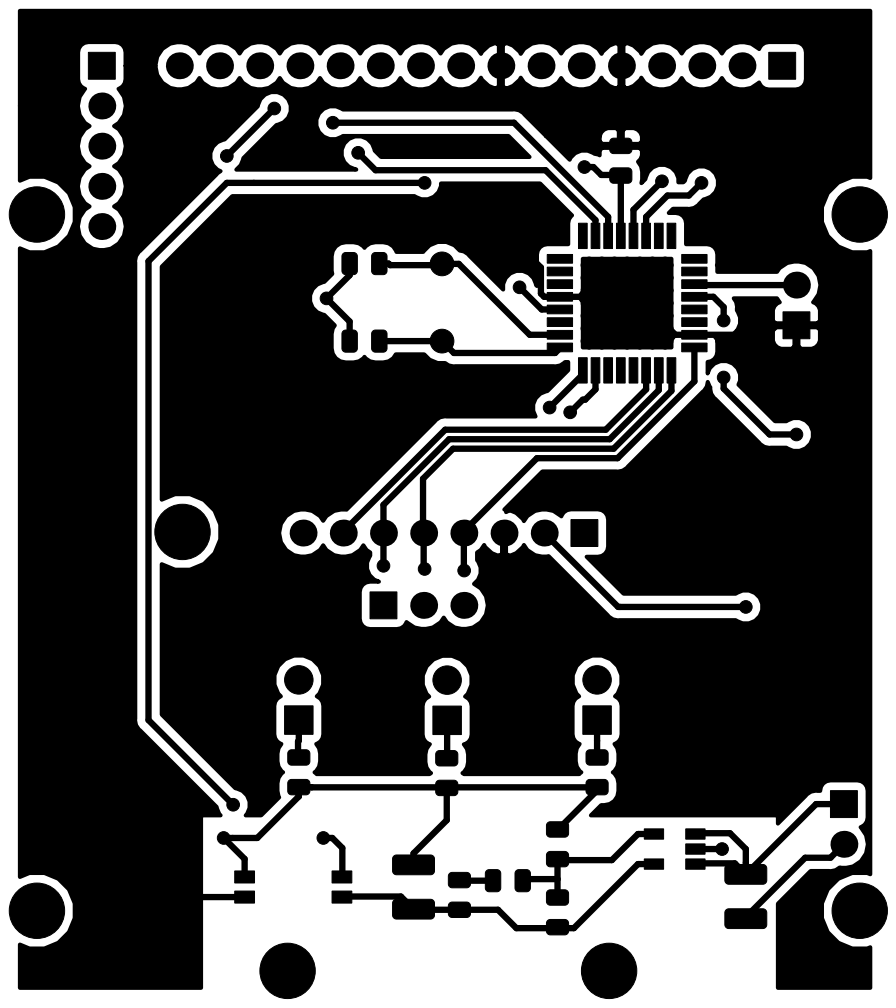
[picture p85: page 1]
