BaileyBrookes/Part_IIB_Project/AircraftDataLogger/Manufacture Files v3/AircraftDataLogger-B.Cu.pdf

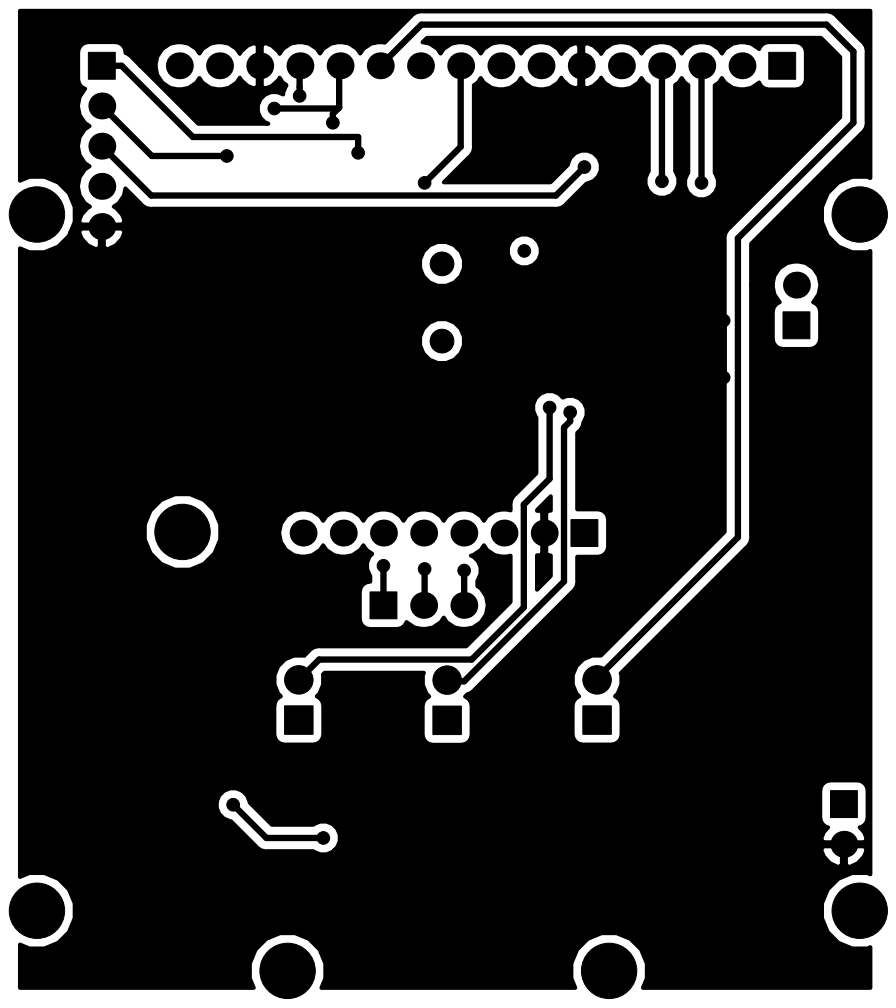
[picture p86: page 1]
