BaileyBrookes/Part_IIB_Project/AircraftDataLogger/Manufacture Files v3/AircraftDataLogger-B.Mask.pdf

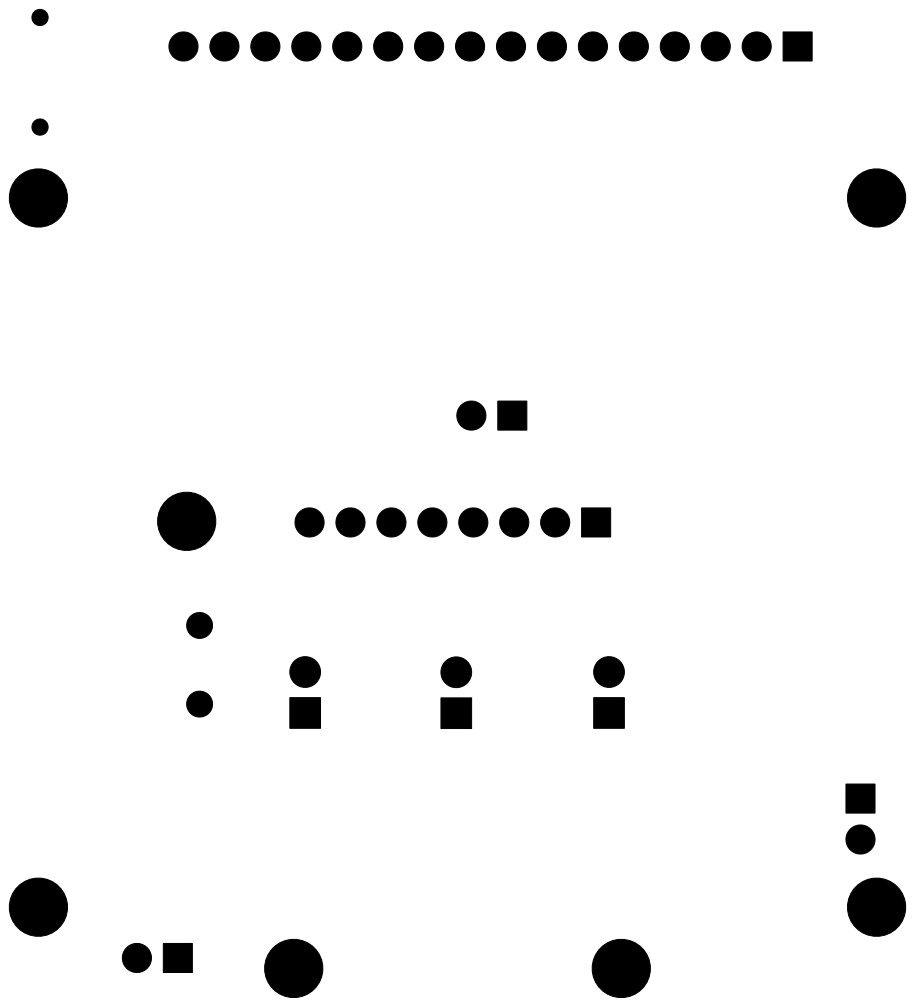
[picture p87: page 1]
