BaileyBrookes/Part_IIB_Project/AircraftDataLogger/Manufacture Files v3/AircraftDataLogger-F.Cu.pdf

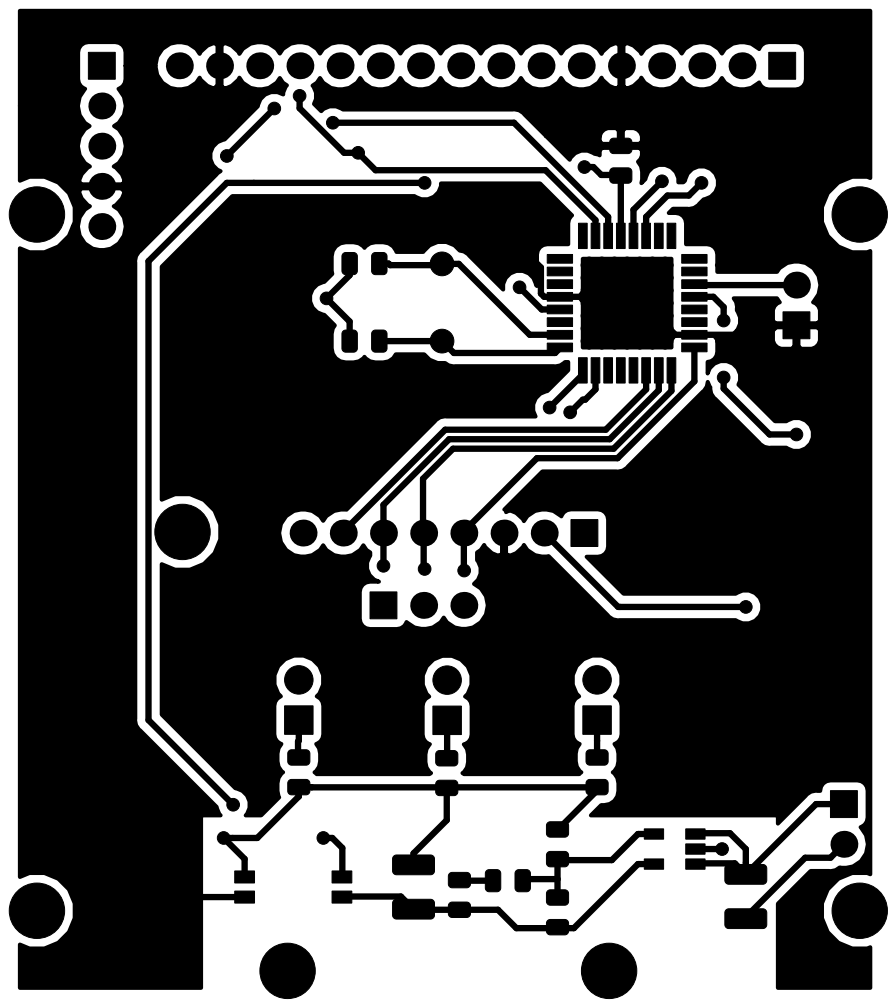
[picture p88: page 1]
